arivvid27/vBoard/Matrix Mapping.png

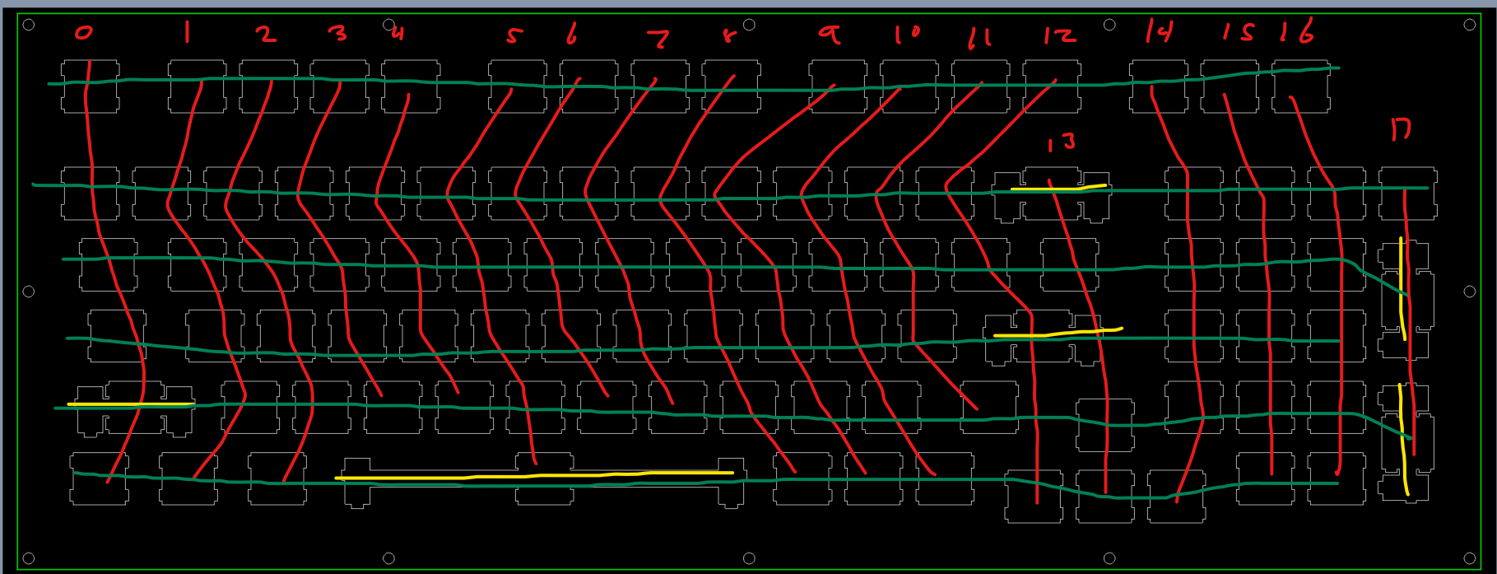
Matrix Mapping.png
