arivvid27/vBoard/CAD FILES/botplate.dxf

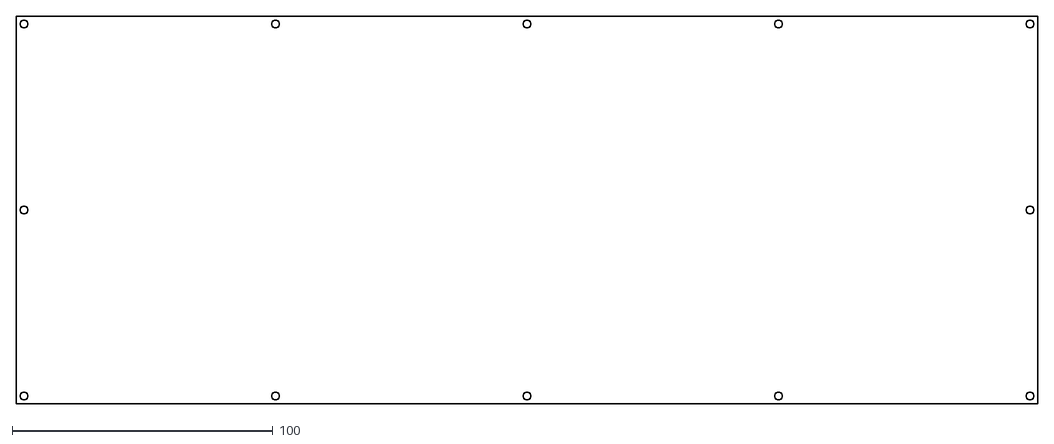
[picture p16: CAD file, 2026-09-21]
CAD FILES/botplate.dxf
391.5 x 148.6
